Artemia76/Ham-ESP32-RPT/include/timer.hpp

/**
 * @file timer.hpp
 * @author Gianni Peschiutta (F4IKZ)
 * @brief HAM-ESP32-RPT
 * @version 0.1
 * @date 2026-02-26
 * 
 * @copyright Copyright (c) 2026
 *
 * 
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
 *    You should have received a copy of the GNU General Public License
 * along with this program.  If not, see <https://www.gnu.org/licenses/>
 */

#ifndef TIMER_HPP
#define TIMER_HPP

#include <Arduino.h>
#include <functional>

/**
 * @brief Handle Timer with callback
 * @details This class purpose simple timer with preselection to callback user
 *          class Method with possibility to one shot or repeat mode 
 * 
 */
class CTimer
{
private:
  /**
   * @brief Callback type method
   * 
   */
  typedef std::function<void()> TimerCallback;

  /**
   * @brief Memory to Callback User class method
   * 
   */
  TimerCallback _Callback;
  uint32_t _interval;
  bool _oneShot;
  bool _running;
	uint32_t _previousMillis;

public:

  /**
   * @brief CTimer constructor
   *
   * @param pInterval : Timer duration in msec
   * @param pCallBack : CallBack method address :
   *            Usage exemple : std::bind(&Class::CallbackMethod,this)
   * @param pOneShot : (Optional) If true , trig once a time the timer
   *                  If False, by default restart timer after each callback
   */
  CTimer (unsigned long pInterval, TimerCallback pCallBack,bool pOneShot=false);

  /**
   * @brief Destroy the CTimer object
   * 
   */
  ~CTimer(){}

  /**
   * @brief Update the timer and trig the callback if Interval reached
   * 
   */
  void Update();

  /**
   * @brief Start the timer for the last duration Interval
   * 
   */
  void Start();

  /**
   * @brief Start the timer for the interval in parameters and recall mode
   * 
   * @param pInterval : Interval duration ine millisecond
   * @param pOneShot : Call one shot the callback if true
   */
  void Start(unsigned long pInterval,bool pOneShot=false );

  /**
   * @brief Stop the timer
   * 
   */
  void Stop();

  /**
   * @brief Return Timer State
   * 
   * @return true : The timer running
   * @return false : The timer stopped
   */
  bool IsRunning();
};

#endif //TIMER_HPP
