Artemia76/Ham-ESP32-RPT/include/webserver.hpp

/**
 * @file webserver.hpp
 * @author Gianni Peschiutta (F4IKZ)
 * @brief HAM-ESP32-RPT
 * @version 0.1
 * @date 2025-02-13
 * 
 * @copyright Copyright (c) 2025
 *
 * 
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
 *    You should have received a copy of the GNU General Public License
 * along with this program.  If not, see <https://www.gnu.org/licenses/>
 */

#ifndef WEBSERVER_HPP
#define WEBSERVER_HPP

#include <ESPAsyncWebServer.h>
#include <vector>
#include <WiFi.h>

#include "appevent.hpp"
#include "timer.hpp"
#include "webserverevent.hpp"
#include "log.hpp"
#include "singleton.hpp"


/**
 * @brief Container for event clients
 * 
 */
typedef std::vector<CWebServerEvent*> v_WebServerSubscribers;

/**
 * @brief WebServer to serv frontend HTML website 
 * 
 * 
 */
class CWebServer : public CSingleTon<CWebServer>, CAppEvent
{
    friend class CWebServerEvent;
    friend class CSingleTon<CWebServer>;
public:


protected:

    /**
    * @brief Background Update event 
    * 
    */
    void OnUpdate();

static void CB_WiFiStationConnected(WiFiEvent_t event, WiFiEventInfo_t info);
    void WiFiStationConnected(WiFiEvent_t event, WiFiEventInfo_t info);

static void CB_WiFiGotIP(WiFiEvent_t event, WiFiEventInfo_t info);
    void WiFiGotIP(WiFiEvent_t event, WiFiEventInfo_t info);

static void CB_WiFiStationDisconnected(WiFiEvent_t event, WiFiEventInfo_t info);
    void WiFiStationDisconnected(WiFiEvent_t event, WiFiEventInfo_t info);

private:

    /**
     * @brief Construct a new CWebServer object
     * 
     */
    CWebServer ();

    /**
     * @brief Destroy the CWebServer object
     * 
     */
    ~CWebServer ();

    /**
     * @brief Suscribers container for loop event
     * 
     */
    v_WebServerSubscribers _subscribers;

    /**
     * @brief Web Server 
     * 
     */
    AsyncWebServer _server;

    CTimer _t1s;

    CTimer _t30s;

    /**
     * @brief Log Controller
     * 
     */
    CLog* _log;

    // Wifi credential
    const char* _ssid;
    const char* _password;

    // Init State
    bool _initialized;
    /**
     * @brief Suscribe to webserver events
     * 
     * @param pSubscriber 
     */
    void _subscribe (CWebServerEvent* pSubscriber);

    /**
     * @brief Unsuscribe to webserver events
     * 
     * @param pSubscriber 
     */
    void _unSubscribe (CWebServerEvent* pSubscriber);
    void OnTimer1S ();
    void OnTimer30S ();
};

#endif //WEBSERVER_HPP
